HL65536/picoDSO/Software/picoDSO240/DisplayST7789_framebuf_3bit.h

#ifndef SRC_DisplayST7789_FRAMEBUF_3bit_H_
#define SRC_DisplayST7789_FRAMEBUF_3bit_H_

#include <SPI.h>
#include <Adafruit_GFX.h>
#include "DisplayST7789.h"
#include <Arduino.h>
#include "shortNames.h"
#include "DisplayCommon.h"

// NEEDS 15KB RAM

#define COLOR3BIT_BLACK 0

#define COLOR3BIT_BLUE 1
#define COLOR3BIT_GREEN 2
#define COLOR3BIT_RED 4

#define COLOR3BIT_CYAN 3
#define COLOR3BIT_MAGENTA 5
#define COLOR3BIT_YELLOW 6

#define COLOR3BIT_WHITE 7
extern u16 colorLookup3bit[];

class VirtualCanvasST7789_3bit : public Adafruit_GFX
{
public:
    u32 framebuf[ST7789_HEIGHT * ST7789_WIDTH / 10]; // 10 pixels in u32

    //for performance reasons, the color argument is the index of the color (as defined above), not the color itself
    void drawPixel(int16_t x, int16_t y, uint16_t color) override;

    VirtualCanvasST7789_3bit();
};

class DisplayST7789_3bit : public DisplayST7789
{
public:
    VirtualCanvasST7789_3bit canvas;

#ifdef ARDUINO_ARCH_RP2040
    DisplayST7789_3bit(u8 DC_pin, u8 RST_pin, i16 DA_pin, i16 CL_PIN, i16 PowerPin1 = -1, i16 PowerPin2 = -1, i16 BL_pin = -1, i16 RX_pin_dummy = -1, SPIClassRP2040 *spi = &SPI);
#else
    // code for different boards here
    DisplayST7789_3bit(u8 DC_pin, u8 RST_pin, i16 DA_pin, i16 CL_PIN, i16 PowerPin1 = -1, i16 PowerPin2 = -1, i16 BL_pin = -1, i16 RX_pin_dummy = -1, SPIClass *spi = &SPI);
#endif

    void startDrawing(u8 textSize = 2) override; // clears screen + other setup work
    // call these in the main loop before/after drawing
    void endDrawing() override; // makes sure the drawed things are actually displayed


    Adafruit_GFX &getGFX() override;
};
#endif /* SRC_DisplayST7789_FRAMEBUF_3bit_H_ */
